jgilje/reveller/sidplayer/c64emu/basic.901226-01.h

 0x94, 0xe3, 0x7b, 0xe3, 0x43, 0x42, 0x4d, 0x42, 
 0x41, 0x53, 0x49, 0x43, 0x30, 0xa8, 0x41, 0xa7, 
 0x1d, 0xad, 0xf7, 0xa8, 0xa4, 0xab, 0xbe, 0xab, 
 0x80, 0xb0, 0x05, 0xac, 0xa4, 0xa9, 0x9f, 0xa8, 
 0x70, 0xa8, 0x27, 0xa9, 0x1c, 0xa8, 0x82, 0xa8, 
 0xd1, 0xa8, 0x3a, 0xa9, 0x2e, 0xa8, 0x4a, 0xa9, 
 0x2c, 0xb8, 0x67, 0xe1, 0x55, 0xe1, 0x64, 0xe1, 
 0xb2, 0xb3, 0x23, 0xb8, 0x7f, 0xaa, 0x9f, 0xaa, 
 0x56, 0xa8, 0x9b, 0xa6, 0x5d, 0xa6, 0x85, 0xaa, 
 0x29, 0xe1, 0xbd, 0xe1, 0xc6, 0xe1, 0x7a, 0xab, 
 0x41, 0xa6, 0x39, 0xbc, 0xcc, 0xbc, 0x58, 0xbc, 
 0x10, 0x03, 0x7d, 0xb3, 0x9e, 0xb3, 0x71, 0xbf, 
 0x97, 0xe0, 0xea, 0xb9, 0xed, 0xbf, 0x64, 0xe2, 
 0x6b, 0xe2, 0xb4, 0xe2, 0x0e, 0xe3, 0x0d, 0xb8, 
 0x7c, 0xb7, 0x65, 0xb4, 0xad, 0xb7, 0x8b, 0xb7, 
 0xec, 0xb6, 0x00, 0xb7, 0x2c, 0xb7, 0x37, 0xb7, 
 0x79, 0x69, 0xb8, 0x79, 0x52, 0xb8, 0x7b, 0x2a, 
 0xba, 0x7b, 0x11, 0xbb, 0x7f, 0x7a, 0xbf, 0x50, 
 0xe8, 0xaf, 0x46, 0xe5, 0xaf, 0x7d, 0xb3, 0xbf, 
 0x5a, 0xd3, 0xae, 0x64, 0x15, 0xb0, 0x45, 0x4e, 
 0xc4, 0x46, 0x4f, 0xd2, 0x4e, 0x45, 0x58, 0xd4, 
 0x44, 0x41, 0x54, 0xc1, 0x49, 0x4e, 0x50, 0x55, 
 0x54, 0xa3, 0x49, 0x4e, 0x50, 0x55, 0xd4, 0x44, 
 0x49, 0xcd, 0x52, 0x45, 0x41, 0xc4, 0x4c, 0x45, 
 0xd4, 0x47, 0x4f, 0x54, 0xcf, 0x52, 0x55, 0xce, 
 0x49, 0xc6, 0x52, 0x45, 0x53, 0x54, 0x4f, 0x52, 
 0xc5, 0x47, 0x4f, 0x53, 0x55, 0xc2, 0x52, 0x45, 
 0x54, 0x55, 0x52, 0xce, 0x52, 0x45, 0xcd, 0x53, 
 0x54, 0x4f, 0xd0, 0x4f, 0xce, 0x57, 0x41, 0x49, 
 0xd4, 0x4c, 0x4f, 0x41, 0xc4, 0x53, 0x41, 0x56, 
 0xc5, 0x56, 0x45, 0x52, 0x49, 0x46, 0xd9, 0x44, 
 0x45, 0xc6, 0x50, 0x4f, 0x4b, 0xc5, 0x50, 0x52, 
 0x49, 0x4e, 0x54, 0xa3, 0x50, 0x52, 0x49, 0x4e, 
 0xd4, 0x43, 0x4f, 0x4e, 0xd4, 0x4c, 0x49, 0x53, 
 0xd4, 0x43, 0x4c, 0xd2, 0x43, 0x4d, 0xc4, 0x53, 
 0x59, 0xd3, 0x4f, 0x50, 0x45, 0xce, 0x43, 0x4c, 
 0x4f, 0x53, 0xc5, 0x47, 0x45, 0xd4, 0x4e, 0x45, 
 0xd7, 0x54, 0x41, 0x42, 0xa8, 0x54, 0xcf, 0x46, 
 0xce, 0x53, 0x50, 0x43, 0xa8, 0x54, 0x48, 0x45, 
 0xce, 0x4e, 0x4f, 0xd4, 0x53, 0x54, 0x45, 0xd0, 
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
