jgilje/reveller/sidplayer/c64emu/kernal.901227-03.h

 0x85, 0x56, 0x20, 0x0f, 0xbc, 0xa5, 0x61, 0xc9, 
 0x88, 0x90, 0x03, 0x20, 0xd4, 0xba, 0x20, 0xcc, 
 0xbc, 0xa5, 0x07, 0x18, 0x69, 0x81, 0xf0, 0xf3, 
 0x38, 0xe9, 0x01, 0x48, 0xa2, 0x05, 0xb5, 0x69, 
 0xb4, 0x61, 0x95, 0x61, 0x94, 0x69, 0xca, 0x10, 
 0xf5, 0xa5, 0x56, 0x85, 0x70, 0x20, 0x53, 0xb8, 
 0x20, 0xb4, 0xbf, 0xa9, 0xc4, 0xa0, 0xbf, 0x20, 
 0x59, 0xe0, 0xa9, 0x00, 0x85, 0x6f, 0x68, 0x20, 
 0xb9, 0xba, 0x60, 0x85, 0x71, 0x84, 0x72, 0x20, 
 0xca, 0xbb, 0xa9, 0x57, 0x20, 0x28, 0xba, 0x20, 
 0x5d, 0xe0, 0xa9, 0x57, 0xa0, 0x00, 0x4c, 0x28, 
 0xba, 0x85, 0x71, 0x84, 0x72, 0x20, 0xc7, 0xbb, 
 0xb1, 0x71, 0x85, 0x67, 0xa4, 0x71, 0xc8, 0x98, 
 0xd0, 0x02, 0xe6, 0x72, 0x85, 0x71, 0xa4, 0x72, 
 0x20, 0x28, 0xba, 0xa5, 0x71, 0xa4, 0x72, 0x18, 
 0x69, 0x05, 0x90, 0x01, 0xc8, 0x85, 0x71, 0x84, 
 0x72, 0x20, 0x67, 0xb8, 0xa9, 0x5c, 0xa0, 0x00, 
 0xc6, 0x67, 0xd0, 0xe4, 0x60, 0x98, 0x35, 0x44, 
 0x7a, 0x00, 0x68, 0x28, 0xb1, 0x46, 0x00, 0x20, 
 0x2b, 0xbc, 0x30, 0x37, 0xd0, 0x20, 0x20, 0xf3, 
 0xff, 0x86, 0x22, 0x84, 0x23, 0xa0, 0x04, 0xb1, 
 0x22, 0x85, 0x62, 0xc8, 0xb1, 0x22, 0x85, 0x64, 
 0xa0, 0x08, 0xb1, 0x22, 0x85, 0x63, 0xc8, 0xb1, 
 0x22, 0x85, 0x65, 0x4c, 0xe3, 0xe0, 0xa9, 0x8b, 
 0xa0, 0x00, 0x20, 0xa2, 0xbb, 0xa9, 0x8d, 0xa0, 
 0xe0, 0x20, 0x28, 0xba, 0xa9, 0x92, 0xa0, 0xe0, 
 0x20, 0x67, 0xb8, 0xa6, 0x65, 0xa5, 0x62, 0x85, 
 0x65, 0x86, 0x62, 0xa6, 0x63, 0xa5, 0x64, 0x85, 
 0x63, 0x86, 0x64, 0xa9, 0x00, 0x85, 0x66, 0xa5, 
 0x61, 0x85, 0x70, 0xa9, 0x80, 0x85, 0x61, 0x20, 
 0xd7, 0xb8, 0xa2, 0x8b, 0xa0, 0x00, 0x4c, 0xd4, 
 0xbb, 0xc9, 0xf0, 0xd0, 0x07, 0x84, 0x38, 0x86, 
 0x37, 0x4c, 0x63, 0xa6, 0xaa, 0xd0, 0x02, 0xa2, 
 0x1e, 0x4c, 0x37, 0xa4, 0x20, 0xd2, 0xff, 0xb0, 
 0xe8, 0x60, 0x20, 0xcf, 0xff, 0xb0, 0xe2, 0x60, 
 0x20, 0xad, 0xe4, 0xb0, 0xdc, 0x60, 0x20, 0xc6, 
 0xff, 0xb0, 0xd6, 0x60, 0x20, 0xe4, 0xff, 0xb0, 
 0xd0, 0x60, 0x20, 0x8a, 0xad, 0x20, 0xf7, 0xb7, 
 0xa9, 0xe1, 0x48, 0xa9, 0x46, 0x48, 0xad, 0x0f, 
 0x03, 0x48, 0xad, 0x0c, 0x03, 0xae, 0x0d, 0x03, 
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
