jgilje/reveller/sidplayer/lcd-hammer.h

#ifndef LCD_H
#define LCD_H

#include <stdint.h>

/* display definitions */
/* 4 lines (hardcoded) */
#define LCD_START_LINE1  0x00     /**< DDRAM address of first char of line 1 */
#define LCD_START_LINE2  0x40     /**< DDRAM address of first char of line 2 */
#define LCD_START_LINE3  0x14     /**< DDRAM address of first char of line 3 */
#define LCD_START_LINE4  0x54     /**< DDRAM address of first char of line 4 */

/* instruction register bit positions, see HD44780U data sheet */
/*
#define LCD_CLR               0
#define LCD_ENTRY_MODE        2
#define LCD_ENTRY_INC         1
*/
#define LCD_DDRAM             7

/* set entry mode: display shift on/off, dec/inc cursor move direction */
#define LCD_ENTRY_DEC            0x04   /* display shift off, dec cursor move dir */
#define LCD_ENTRY_DEC_SHIFT      0x05   /* display shift on,  dec cursor move dir */
#define LCD_ENTRY_INC            0x06   /* display shift off, inc cursor move dir */
#define LCD_ENTRY_INC_SHIFT      0x07   /* display shift on,  inc cursor move dir */

/* display on/off, cursor on/off, blinking char at cursor position */
#define LCD_DISP_CLEAR			 0x01	/* clear display						  */
#define LCD_DISP_OFF             0x08   /* display off                            */
#define LCD_DISP_ON              0x0C   /* display on, cursor off                 */
#define LCD_DISP_ON_BLINK        0x0D   /* display on, cursor off, blink char     */
#define LCD_DISP_ON_CURSOR       0x0E   /* display on, cursor on                  */
#define LCD_DISP_ON_CURSOR_BLINK 0x0F   /* display on, cursor on, blink char      */

/* move cursor/shift display */
#define LCD_MOVE_CURSOR_HOME	0x02

/* function set: set interface data length and number of display lines */
#define LCD_FUNCTION_4BIT_2LINES 0x28   /* 4-bit interface, dual line,   5x7 dots */

#define LCD_MODE_DEFAULT     ((1<<LCD_ENTRY_MODE) | (1<<LCD_ENTRY_INC) )
#define LCD_FUNCTION_DEFAULT    LCD_FUNCTION_4BIT_2LINES 

void lcd_init(void);
void lcd_clear(void);
void lcd_puts(const char *s);
void lcd_print_lines(char** line_v, int lines);
void lcd_gotoxy(uint8_t x, uint8_t y);
void lcd_reinit(uint32_t e_delay_t, uint32_t r_delay_t);

#endif
