jgilje/reveller/qt-gui/mainwindow.cpp

#include <QJsonArray>
#include <QJsonValue>
#include <QJsonObject>
#include <QJsonDocument>

#include "mainwindow.h"
#include "ui_mainwindow.h"
#include "siditem.h"
#include "connectdialog.h"
#include "sidinfo.h"

#include <QSettings>
#include <QMessageBox>

MainWindow::MainWindow(bool &ok, QWidget *parent) :
    QMainWindow(parent),
    ui(new Ui::MainWindow),
    _webSocket(NULL),
    _model(NULL)
{
    ui->setupUi(this);

    SidInfo *info = new SidInfo;
    ui->columnView->setPreviewWidget(info);

    QSettings settings;
    QString url = runConnectionDialog();
    if (! url.startsWith("http://")) {
        url.prepend("http://");
    }
    wsConnect(url);

    connect(ui->labelCurrentSong, &QLabel::linkActivated, this, &MainWindow::onNavigation);
    ok = true;
}

MainWindow::~MainWindow() {
    delete ui;
}

QString MainWindow::runConnectionDialog() {
    QSettings settings;
    ConnectDialog d;
    d.url(settings.value("url").toString());
    int r = d.exec();
    if (r == 0) {
        return "";
    }

    return d.url();
}

void MainWindow::on_actionDisconnect_triggered() {
    qDebug() << Q_FUNC_INFO;
    _webSocket->close();

}

void MainWindow::wsConnect(const QString &address) {
    if (_webSocket != NULL) {
        delete _webSocket;
    }

    QUrl url(address);
    QUrl wsUrl(url);
    wsUrl.setScheme("ws");
    wsUrl.setPath("/ws");

    _webSocket = new QWebSocket(address);
    connect(_webSocket, &QWebSocket::connected, this, &MainWindow::onConnected);
    connect(_webSocket, &QWebSocket::disconnected, this, &MainWindow::onDisconnected);
    connect(_webSocket, &QWebSocket::stateChanged, this, &MainWindow::onWebSocketStateChange);

    _webSocket->open(wsUrl);
}

void MainWindow::onWebSocketStateChange(QAbstractSocket::SocketState state) {
    qDebug() << state;
}

void MainWindow::onConnected() {
    QSettings settings;
    settings.setValue("url", _webSocket->origin());

    connect(_webSocket, &QWebSocket::textMessageReceived, this, &MainWindow::onTextMessageReceived);

    _model = new SidItemModel();
    connect(_model, &SidItemModel::fetchItem, this, &MainWindow::onFetchItem);
    ui->columnView->setModel(_model);

    connect(ui->columnView, &QColumnView::updatePreviewWidget, this, &MainWindow::onUpdatePreview);
    connect(ui->columnView->selectionModel(), &QItemSelectionModel::selectionChanged, this, &MainWindow::onSelectionChanged);

    QJsonObject json;
    json["action"] = "state";
    _webSocket->sendTextMessage(QJsonDocument(json).toJson());
}

void MainWindow::onDisconnected() {
    qDebug() << "WebSocket disconnected";
    _webSocket->close();

    QString url = runConnectionDialog();
    if (url.isEmpty()) {
        qApp->exit(1);
    }

    wsConnect(url);
}

void MainWindow::onTextMessageReceived(QString message) {
    QJsonDocument document = QJsonDocument::fromJson(message.toUtf8());
    QJsonObject root = document.object();
    QString type = root["type"].toString();

    if (type == QStringLiteral("state")) {
        QJsonObject dataObj = root["data"].toObject();
        if (! ui->centralWidget->isEnabled()) {
            ui->centralWidget->setEnabled(true);
        }

        handleState(dataObj);
    } else if (type == QStringLiteral("ls")) {
        QJsonObject dataObj = root["data"].toObject();
        handleLs(dataObj.value("path").toString(), dataObj.value("directories").toArray(), dataObj.value("sidfiles").toArray());
    } else if (type == QStringLiteral("load")) {
        QString data = root["data"].toString();
        handleLoad(data);
    } else if (type == QStringLiteral("currentSidHeader")) {
        QJsonObject dataObj = root["data"].toObject();
        header = SidHeader::parse(dataObj);
        SidInfo *info = qobject_cast<SidInfo*>(ui->columnView->previewWidget());
        info->setHeader(header);
        ui->labelTotalSubsongs->setText(QString::number(header.songs));
    } else if (type == QStringLiteral("crash")) {
        ui->centralWidget->setEnabled(false);
        QMessageBox::warning(this, "Crash!", QString("The SIDPlayer crashed with the following error \"%1\"").arg(root["data"].toString()));
    } else {
        qDebug() << message;
    }
}

void MainWindow::updateNavbar(const QString& file) {
    QString path;
    QStringList filepath = file.split("/");
    QStringList nav;
    foreach (const QString& file, filepath) {
        nav.append(QString("<a href='%1%2'>%2</a>").arg(path).arg(file));
        path.append(file + "/");
    }
    ui->labelCurrentSong->setText(nav.join(" / "));
}

void MainWindow::handleState(const QJsonObject &data) {
    currentFile = data["file"].toString();
    updateNavbar(currentFile);
    ui->labelCurrentState->setText(data["state"].toString() == "play" ? "playing" : "stopped");

    currentSong = data["song"].toInt();
    ui->labelCurrentSubsong->setText(QString::number(currentSong));
}

void MainWindow::handleLs(const QString& path, const QJsonArray &jsonDirectories, const QJsonArray &jsonSidfiles) {
    QStringList directories;
    QStringList sidfiles;

    foreach (const QJsonValue& value, jsonDirectories) {
        directories.append(value.toString());
    }
    foreach (const QJsonValue& value, jsonSidfiles) {
        sidfiles.append(value.toString());
    }

    _model->directoryData(path, directories, sidfiles);
    if (selectPath.size() > 0) {
        resolveSelectPath();
    }
}

void MainWindow::handleLoad(const QString &data) {
    updateNavbar(data);

    if (_setDefaultSong) {
        currentSong = 0;
        songRequest();

        _setDefaultSong = false;
    }
}

void MainWindow::fetchPath(const QString& path) {
    QJsonObject json;
    json["action"] = "ls";
    json["argument"] = path;
    _webSocket->sendTextMessage(QJsonDocument(json).toJson());
}

void MainWindow::onFetchItem(SidItem *item) {
    if (item->hasLoaded()) {
        return;
    }

    fetchPath(item->path());
}

void MainWindow::songRequest() {
    QJsonObject json;
    json["action"] = "song";
    json["argument"] = QString::number(currentSong);
    _webSocket->sendTextMessage(QJsonDocument(json).toJson());
}

void MainWindow::onUpdatePreview(const QModelIndex &index) {
    SidItem *item = _model->itemFromModelIndex(index);

    QJsonObject json;
    json["action"] = "load";
    json["argument"] = item->path();
    _webSocket->sendTextMessage(QJsonDocument(json).toJson());

    _setDefaultSong = true;
}

void MainWindow::onSelectionChanged(const QItemSelection & selected, const QItemSelection & deselected) {
    Q_UNUSED(selected)
    Q_UNUSED(deselected)

    /* Prevents annoying select-all => select actual behaviour when clicking a sid file */
    if (ui->columnView->selectionModel()->selectedIndexes().size() > 0) {
        ui->columnView->selectionModel()->select(ui->columnView->selectionModel()->selectedIndexes().last(), QItemSelectionModel::SelectCurrent);
    }
}

void MainWindow::onNavigation(const QString &link) {
    selectPath.clear();

    QString path;
    QStringList filepath = link.split("/");
    foreach (const QString& file, filepath) {
        selectPath.append(QString("%1%2").arg(path).arg(file));
        path.append(file + "/");
    }

    resolveSelectPath();
}

void MainWindow::resolveSelectPath() {
    QModelIndexList modelIndexList;
    QModelIndex index;

    foreach (const QString& pathItem, selectPath) {
        QModelIndex idx = _model->fromPath(pathItem);
        if (idx.isValid()) {
            SidItem* item = _model->itemFromModelIndex(idx);
            if (item->hasLoaded()) {
                modelIndexList.append(idx);
                index = idx;
                selectPath.removeFirst();
            } else {
                fetchPath(pathItem);
                return;
            }
        } else {
            // TODO this is probably an error!
            fetchPath(pathItem);
            return;
        }
    }

    if (selectPath.isEmpty()) {
        ui->columnView->selectionModel()->setCurrentIndex(index, QItemSelectionModel::ClearAndSelect);
        selectPath.clear();
    }
}

void MainWindow::on_pushButtonPrev_clicked() {
    if (currentSong <= 1) {
        return;
    }

    currentSong--;
    songRequest();
}

void MainWindow::on_pushButtonNext_clicked() {
    if (currentSong >= header.songs) {
        return;
    }

    currentSong++;
    songRequest();
}
